TheCaveCz/kit-traffic-lights/doc/pictures/IMG_7060-Edit.jpg

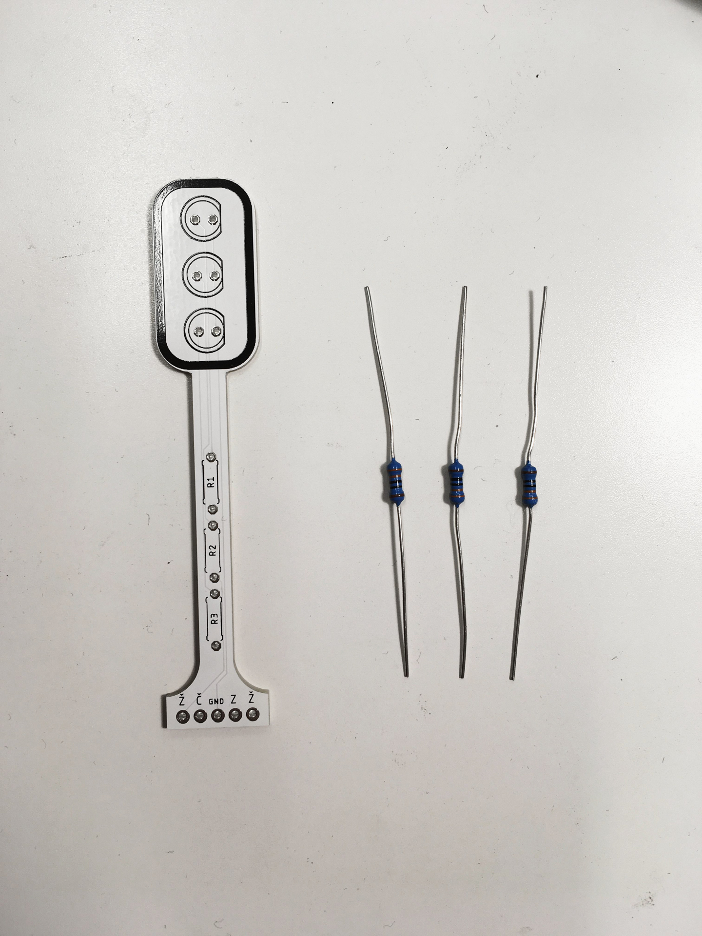
doc/pictures/IMG_7060-Edit.jpg
