TheCaveCz/kit-traffic-lights/doc/pictures/IMG_7062-Edit.jpg

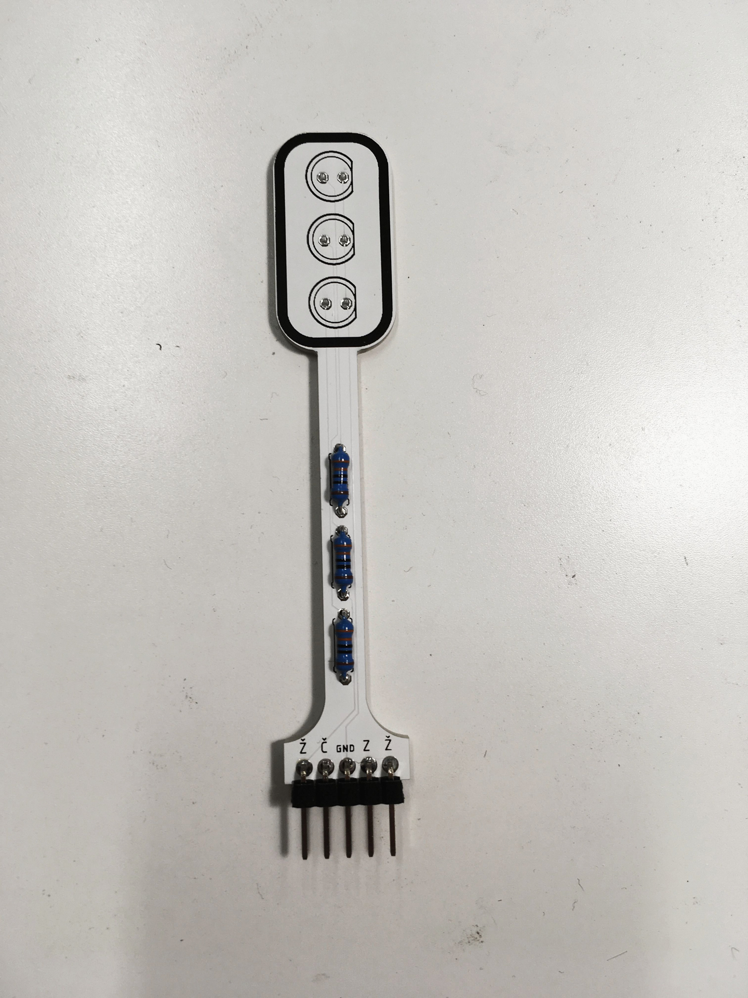
doc/pictures/IMG_7062-Edit.jpg
