TheCaveCz/kit-traffic-lights/doc/pictures/IMG_7063-Edit.jpg

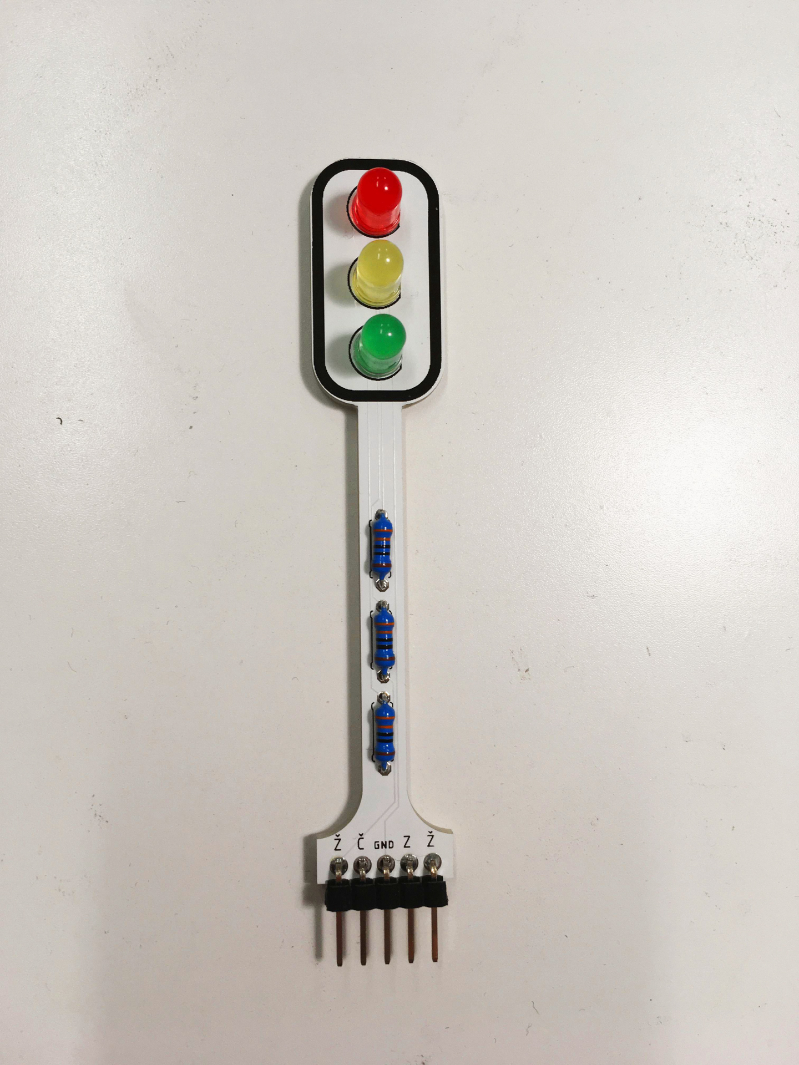
doc/pictures/IMG_7063-Edit.jpg
