TheCaveCz/kit-traffic-lights/doc/pictures/IMG_7064-Edit.jpg

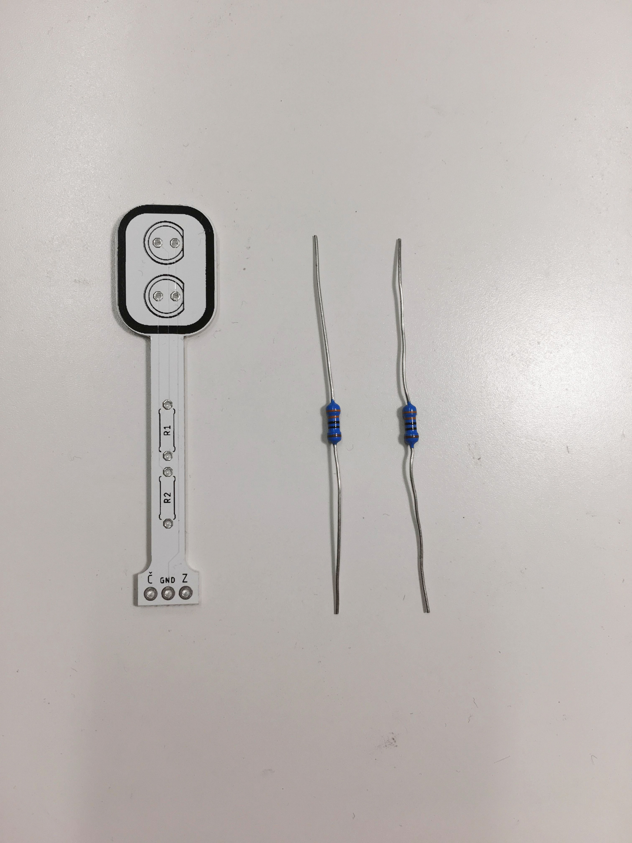
doc/pictures/IMG_7064-Edit.jpg
