TheCaveCz/kit-traffic-lights/doc/pictures/IMG_7066-Edit.jpg

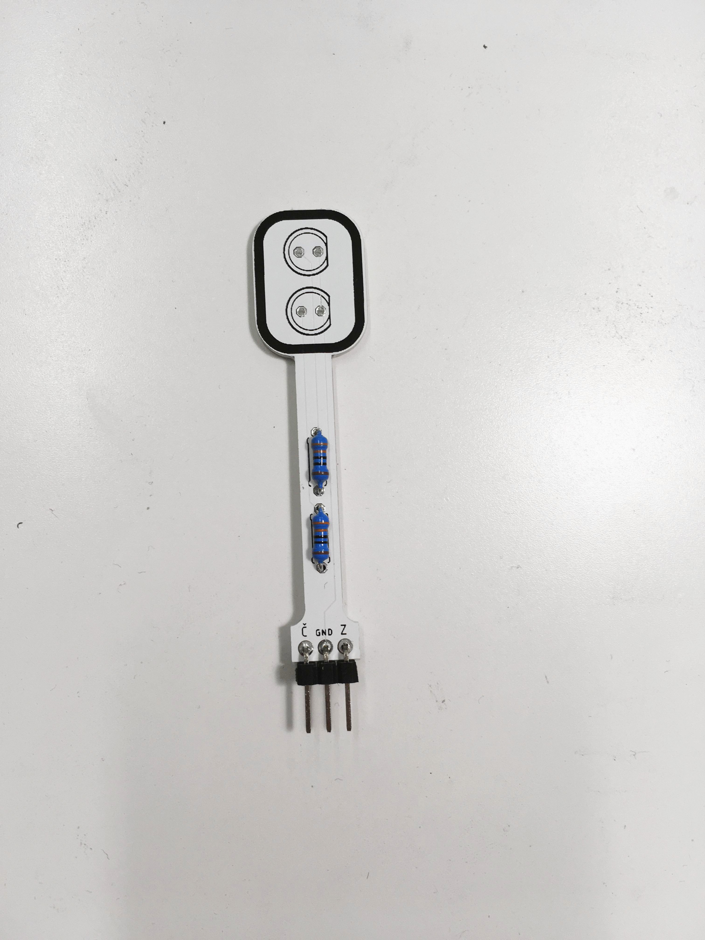
doc/pictures/IMG_7066-Edit.jpg
