TheCaveCz/kit-traffic-lights/doc/pictures/IMG_7067-Edit.jpg

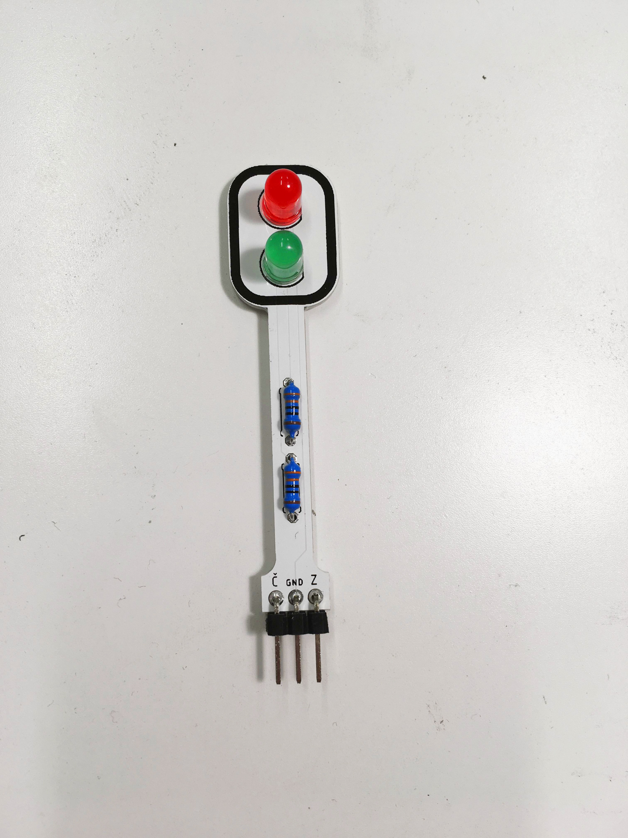
doc/pictures/IMG_7067-Edit.jpg
