TheCaveCz/kit-traffic-lights/doc/pictures/IMG_7068-Edit.jpg

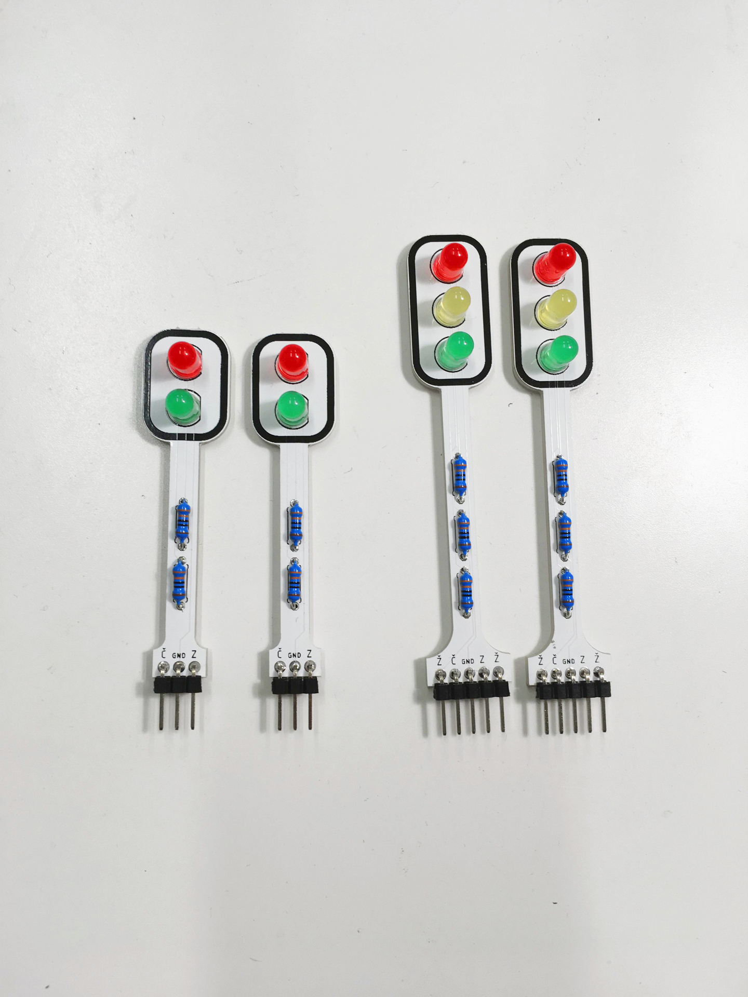
doc/pictures/IMG_7068-Edit.jpg
