TheCaveCz/kit-traffic-lights/doc/pictures/IMG_7071-Edit.jpg

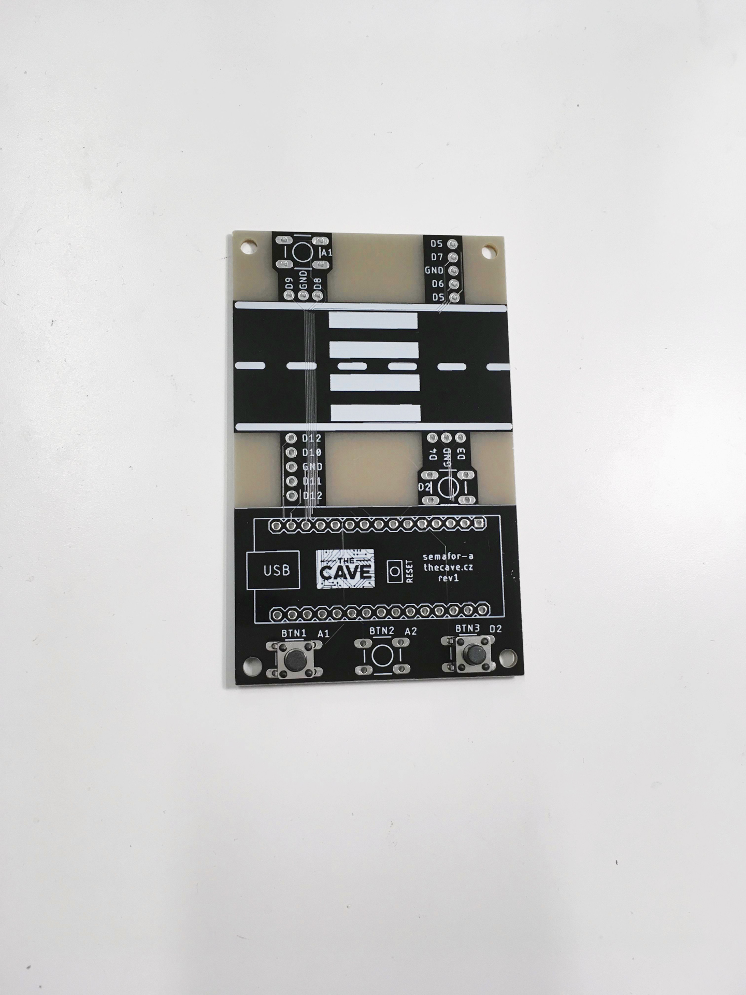
doc/pictures/IMG_7071-Edit.jpg
