TheCaveCz/kit-traffic-lights/doc/pictures/IMG_7073-Edit.jpg

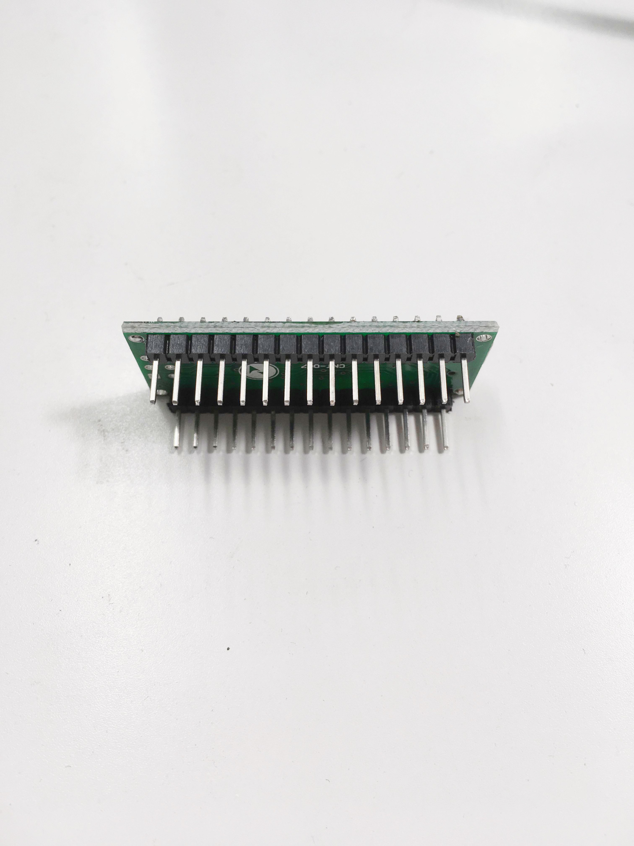
doc/pictures/IMG_7073-Edit.jpg
