TheCaveCz/kit-traffic-lights/doc/pictures/IMG_7075-Edit.jpg

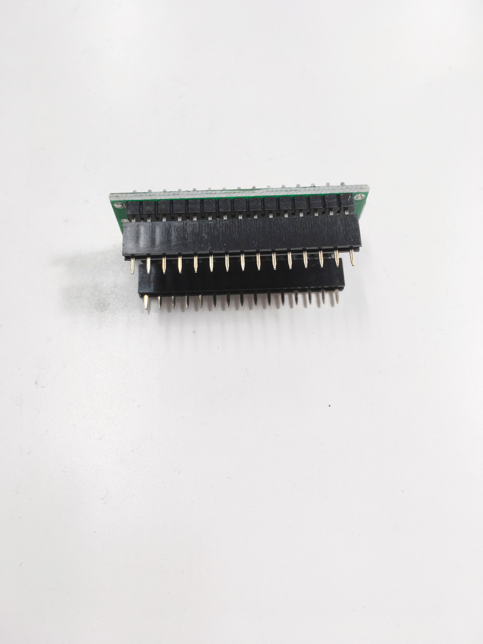
doc/pictures/IMG_7075-Edit.jpg
