TheCaveCz/kit-traffic-lights/doc/pictures/IMG_7076-Edit.jpg

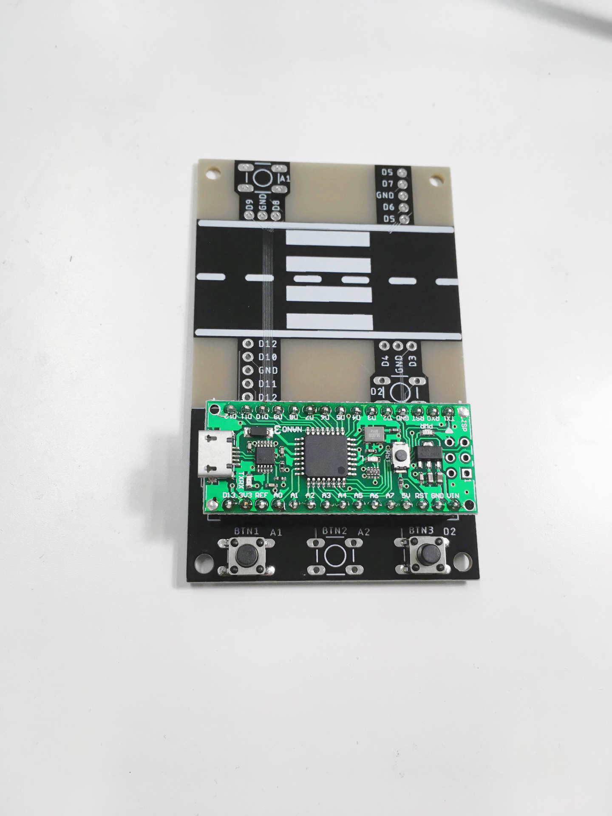
doc/pictures/IMG_7076-Edit.jpg
