TheCaveCz/kit-traffic-lights/doc/pictures/IMG_7077-Edit.jpg

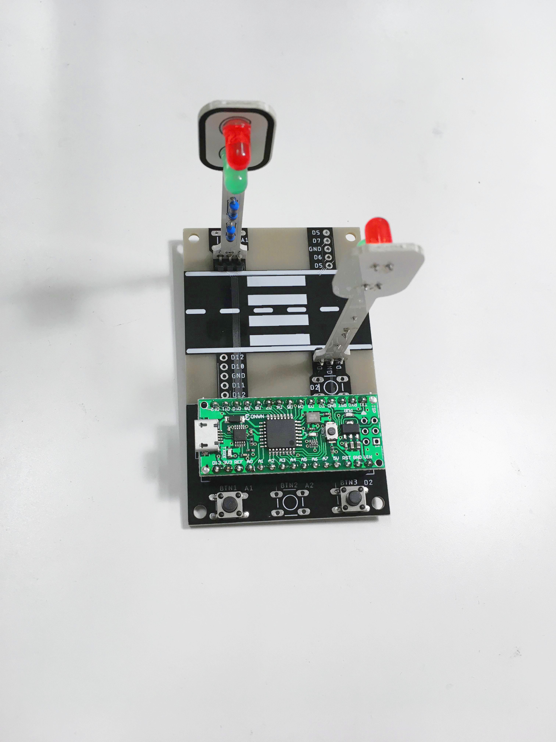
doc/pictures/IMG_7077-Edit.jpg
