TheCaveCz/kit-traffic-lights/doc/pictures/IMG_7079-Edit.jpg

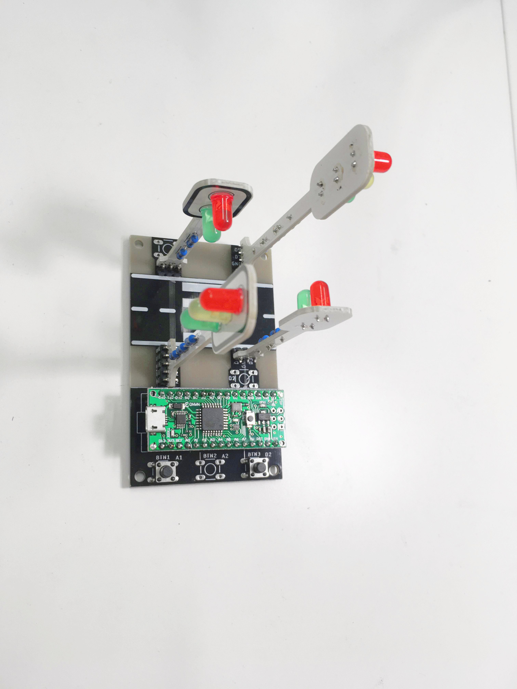
doc/pictures/IMG_7079-Edit.jpg
